NicolasJao/MIST/RESOURCES/IMAGES/3D VIEWER/PCB back.png

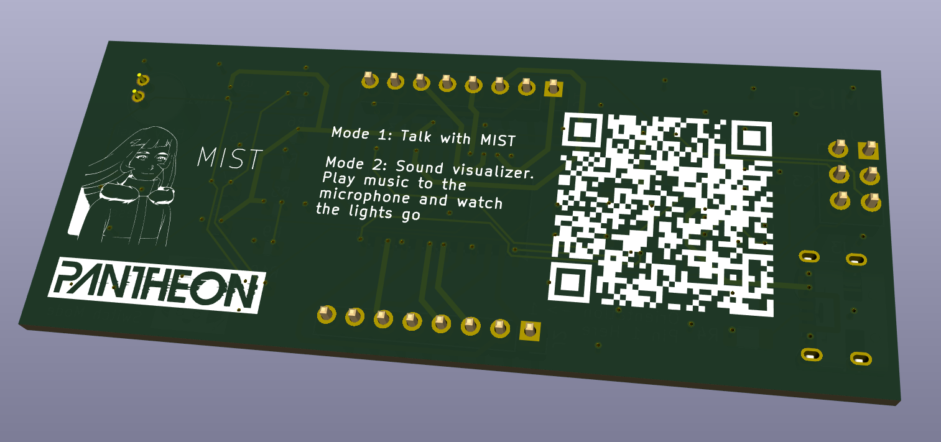
RESOURCES/IMAGES/3D VIEWER/PCB back.png
