NicolasJao/MIST/RESOURCES/IMAGES/3D VIEWER/PCB front.png

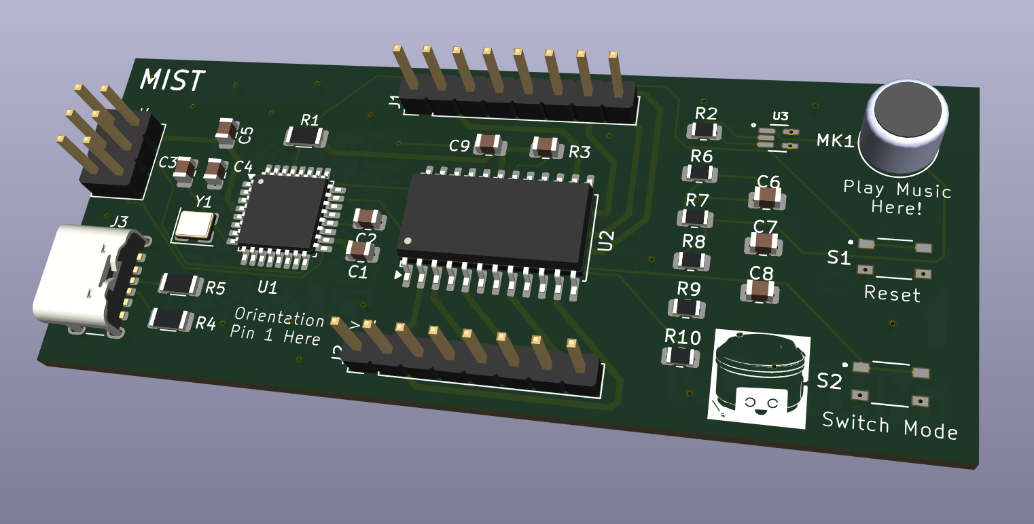
RESOURCES/IMAGES/3D VIEWER/PCB front.png
