NicolasJao/MIST/RESOURCES/IMAGES/SILKSCREEN/MIST CI 2.png

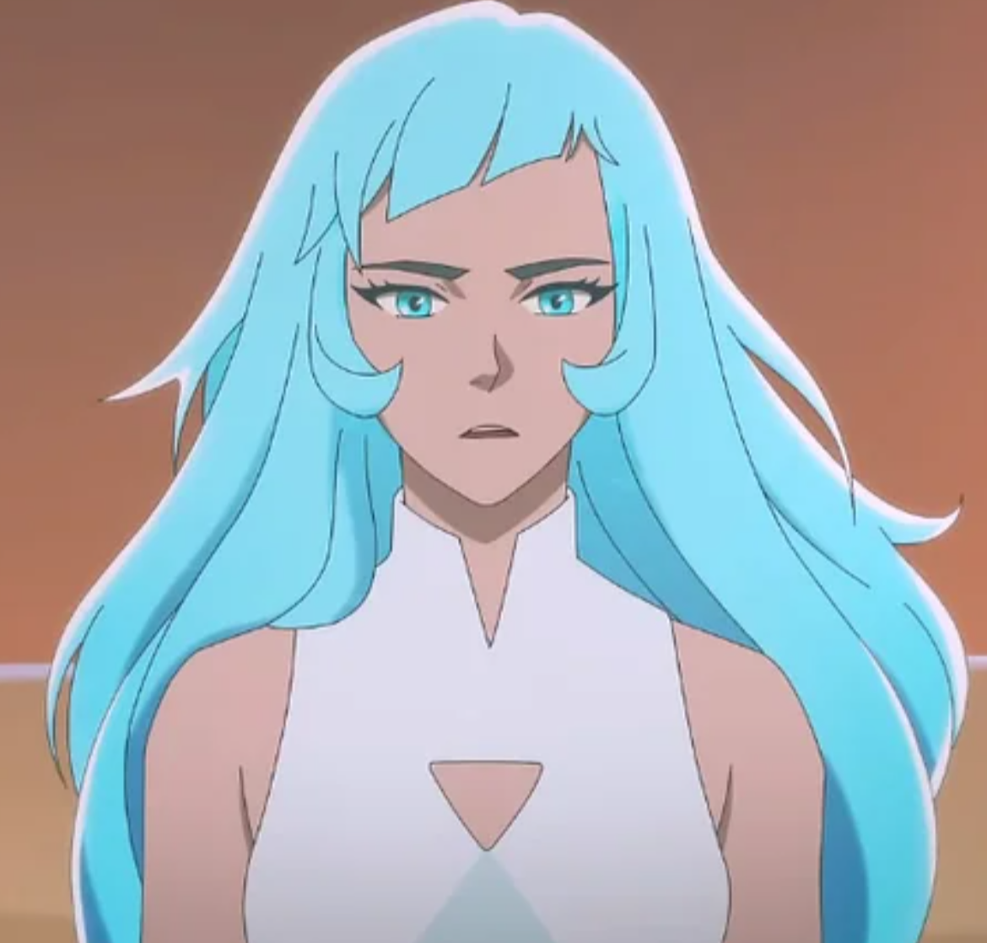
RESOURCES/IMAGES/SILKSCREEN/MIST CI 2.png
