NicolasJao/MIST/RESOURCES/IMAGES/SILKSCREEN/MIST CI bitmap.png

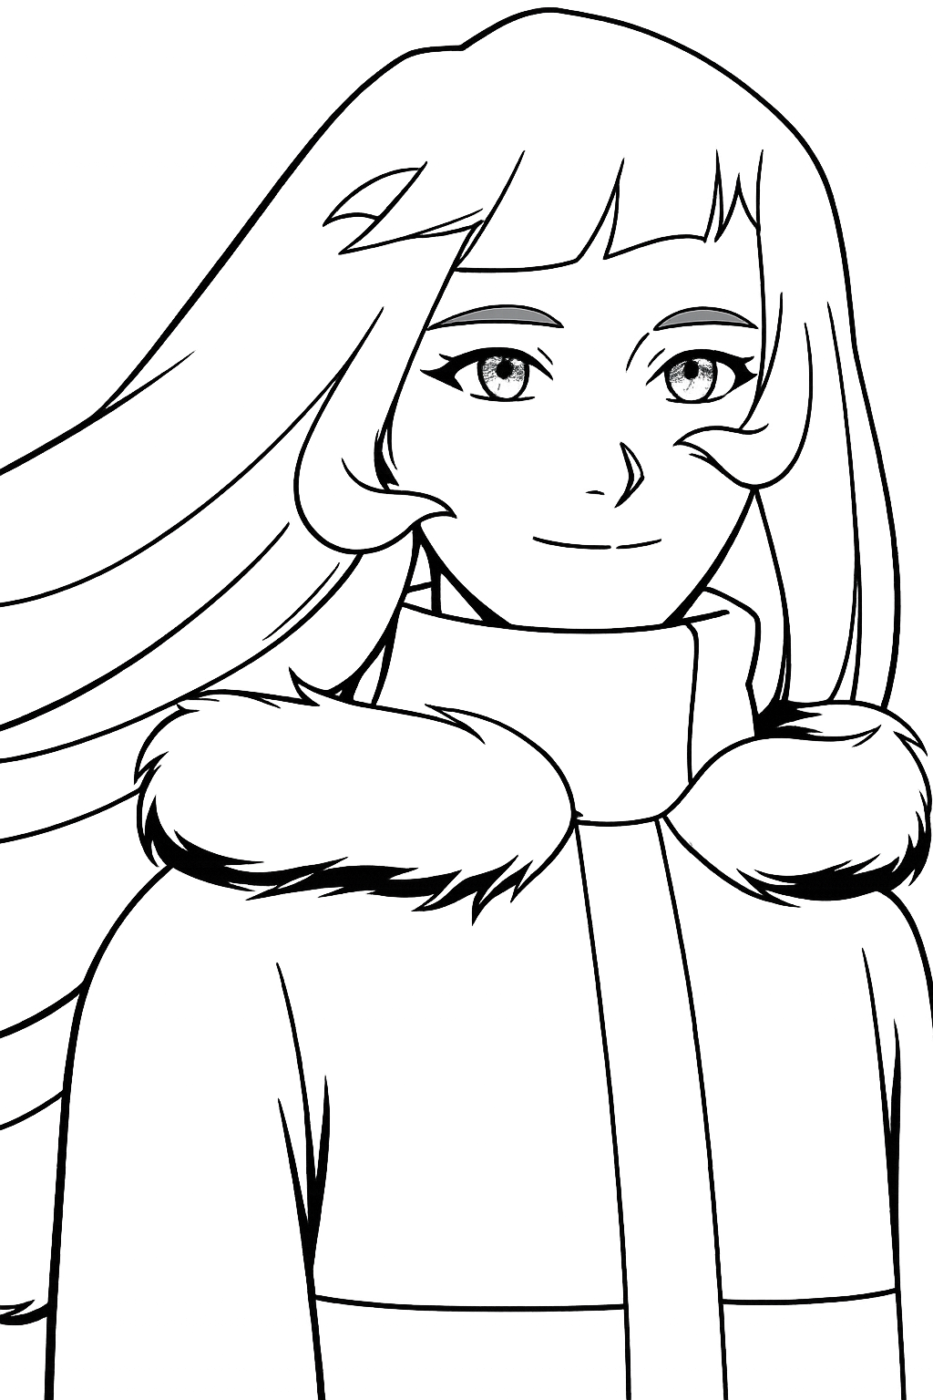
RESOURCES/IMAGES/SILKSCREEN/MIST CI bitmap.png
