NicolasJao/MIST/RESOURCES/IMAGES/SILKSCREEN/MIST happy.png

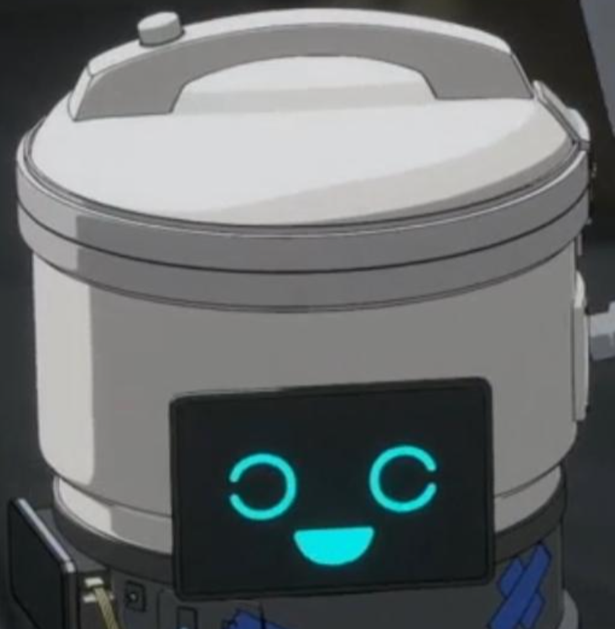
RESOURCES/IMAGES/SILKSCREEN/MIST happy.png
