NicolasJao/MIST/RESOURCES/IMAGES/SILKSCREEN/MIST model.png

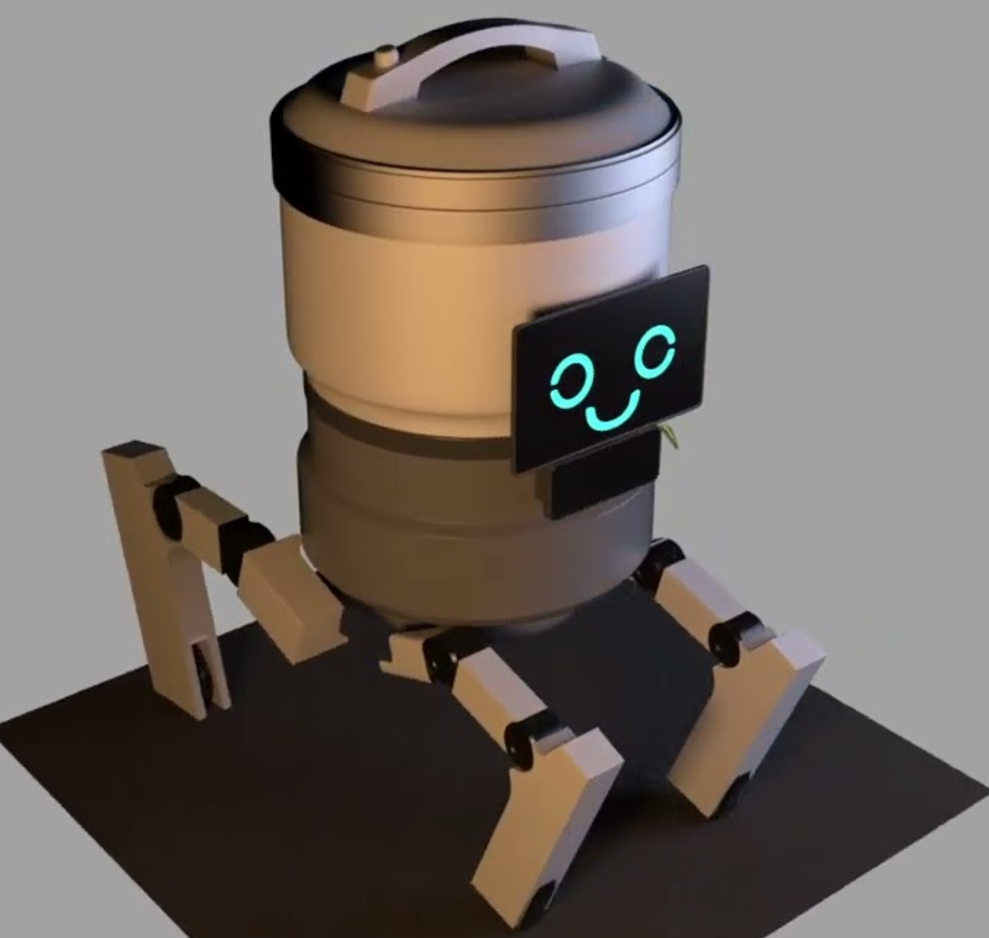
RESOURCES/IMAGES/SILKSCREEN/MIST model.png
