NicolasJao/MIST/RESOURCES/IMAGES/SILKSCREEN/MIST picture.png

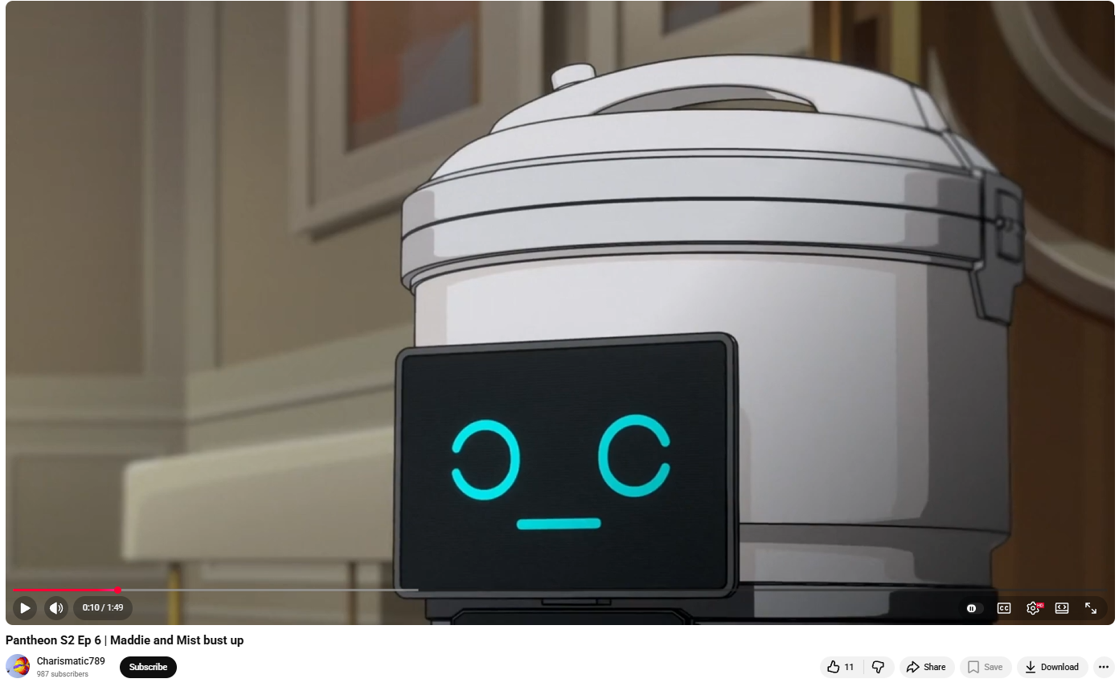
RESOURCES/IMAGES/SILKSCREEN/MIST picture.png
